eduardez/Oledukey/OLEDU_KiCad/OLEDUKEY/OLEDUKEY.csv

Reference | Value | Footprint | Datasheet | Part URL
U1 | STM32F072RBTx | Package_QFP:LQFP-64_10x10mm_P0.5mm | http://www.st.com/st-web-ui/static/active/en/resource/technical/document/datasheet/DM00090510.pdf | https://es.aliexpress.com/item/4001114352067.html
C1 | 100nF | Capacitor_SMD:C_0603_1608Metric_Pad1.08x0.95mm_HandSolder | https://datasheet.lcsc.com/lcsc/1809211526_FH-Guangdong-Fenghua-Advanced-Tech-0603F104M500NT_C42998.pdf | https://lcsc.com/product-detail/Multilayer-Ceramic-Capacitors-MLCC-SMD-SMT_FH-Guangdong-Fenghua-Advanced-Tech-0603F104M500NT_C42998.html
SW93 | Rotary_Encoder_Switch | Rotary_Encoder:RotaryEncoder_Alps_EC11E-Switch_Vertical_H20mm | https://www.farnell.com/datasheets/1837001.pdf | https://es.aliexpress.com/item/1744383771.html
C2 | 100nF | Capacitor_SMD:C_0603_1608Metric_Pad1.08x0.95mm_HandSolder | https://datasheet.lcsc.com/lcsc/1809211526_FH-Guangdong-Fenghua-Advanced-Tech-0603F104M500NT_C42998.pdf | https://lcsc.com/product-detail/Multilayer-Ceramic-Capacitors-MLCC-SMD-SMT_FH-Guangdong-Fenghua-Advanced-Tech-0603F104M500NT_C42998.html
SW92 | SW_Push | Button_Switch_SMD:SW_SPST_TL3342 | https://datasheet.lcsc.com/lcsc/2109061530_E-Switch-TL3342F160QG_C2886898.pdf | https://lcsc.com/product-detail/Tactile-Switches_E-Switch-TL3342F160QG_C2886898.html
R1 | 10k | Resistor_THT:R_Axial_DIN0204_L3.6mm_D1.6mm_P7.62mm_Horizontal | ~ | Home
C3 | 100nF | Capacitor_SMD:C_0603_1608Metric_Pad1.08x0.95mm_HandSolder | https://datasheet.lcsc.com/lcsc/1809211526_FH-Guangdong-Fenghua-Advanced-Tech-0603F104M500NT_C42998.pdf | https://lcsc.com/product-detail/Multilayer-Ceramic-Capacitors-MLCC-SMD-SMT_FH-Guangdong-Fenghua-Advanced-Tech-0603F104M500NT_C42998.html
SW91 | SW_Push | Button_Switch_SMD:SW_SPST_TL3342 | https://datasheet.lcsc.com/lcsc/2109061530_E-Switch-TL3342F160QG_C2886898.pdf | https://lcsc.com/product-detail/Tactile-Switches_E-Switch-TL3342F160QG_C2886898.html
R3 | 5.1k | Resistor_THT:R_Axial_DIN0204_L3.6mm_D1.6mm_P7.62mm_Horizontal | ~ | Home
R2 | 5.1k | Resistor_THT:R_Axial_DIN0204_L3.6mm_D1.6mm_P7.62mm_Horizontal | ~ | Home
J1 | USB_C_TYPE-C-31-M-12 | Connector_USB:USB_C_Receptacle_HRO_TYPE-C-31-M-12 | https://datasheet.lcsc.com/lcsc/2108131730_Korean-Hroparts-Elec-TYPE-C-31-M-12_C165948.pdf | https://lcsc.com/product-detail/USB-Connectors_Korean-Hroparts-Elec-TYPE-C-31-M-12_C165948.html
U2 | 2.42OLED | oLED:DIYMORE.CC |  | https://es.aliexpress.com/item/33023119677.html
SW94 | Rotary_Encoder_Switch | Rotary_Encoder:RotaryEncoder_Alps_EC11E-Switch_Vertical_H20mm | https://www.farnell.com/datasheets/1837001.pdf | https://es.aliexpress.com/item/1744383771.html
U3 | AMS1117-3.3 | Package_TO_SOT_SMD:SOT-223-3_TabPin2 | http://www.advanced-monolithic.com/pdf/ds1117.pdf | https://lcsc.com/product-detail/Linear-Voltage-Regulators-LDO_PUOLOP-AMS1117-3-3_C351784.html
C4 | 10uF | Capacitor_SMD:C_0603_1608Metric_Pad1.08x0.95mm_HandSolder | https://datasheet.lcsc.com/lcsc/1811021421_Samsung-Electro-Mechanics-CL10A106MP8NNNC_C85713.pdf | https://lcsc.com/product-detail/Multilayer-Ceramic-Capacitors-MLCC-SMD-SMT_Samsung-Electro-Mechanics-CL10A106MP8NNNC_C85713.html
C5 | 100nF | Capacitor_SMD:C_0603_1608Metric_Pad1.08x0.95mm_HandSolder | https://datasheet.lcsc.com/lcsc/1809211526_FH-Guangdong-Fenghua-Advanced-Tech-0603F104M500NT_C42998.pdf | https://lcsc.com/product-detail/Multilayer-Ceramic-Capacitors-MLCC-SMD-SMT_FH-Guangdong-Fenghua-Advanced-Tech-0603F104M500NT_C42998.html
C6 | 100nF | Capacitor_SMD:C_0603_1608Metric_Pad1.08x0.95mm_HandSolder | https://datasheet.lcsc.com/lcsc/1809211526_FH-Guangdong-Fenghua-Advanced-Tech-0603F104M500NT_C42998.pdf | https://lcsc.com/product-detail/Multilayer-Ceramic-Capacitors-MLCC-SMD-SMT_FH-Guangdong-Fenghua-Advanced-Tech-0603F104M500NT_C42998.html
C7 | 10uF | Capacitor_SMD:C_0603_1608Metric_Pad1.08x0.95mm_HandSolder | https://datasheet.lcsc.com/lcsc/1811021421_Samsung-Electro-Mechanics-CL10A106MP8NNNC_C85713.pdf | https://lcsc.com/product-detail/Multilayer-Ceramic-Capacitors-MLCC-SMD-SMT_Samsung-Electro-Mechanics-CL10A106MP8NNNC_C85713.html
RV1 | R_POT | Potentiometer_THT:Potentiometer_Bourns_PTA6043_Single_Slide | https://www.mouser.es/datasheet/2/54/pta-778345.pdf | https://es.aliexpress.com/item/32785393756.html
D311 | SK6812MINI | LED_SDM_MOD:SK6812-MINI-E | https://cdn-shop.adafruit.com/product-files/2686/SK6812MINI_REV.01-1-2.pdf | https://es.aliexpress.com/item/32782295214.html
D310 | SK6812MINI | LED_SDM_MOD:SK6812-MINI-E | https://cdn-shop.adafruit.com/product-files/2686/SK6812MINI_REV.01-1-2.pdf | https://es.aliexpress.com/item/32782295214.html
D309 | SK6812MINI | LED_SDM_MOD:SK6812-MINI-E | https://cdn-shop.adafruit.com/product-files/2686/SK6812MINI_REV.01-1-2.pdf | https://es.aliexpress.com/item/32782295214.html
D312 | SK6812MINI | LED_SDM_MOD:SK6812-MINI-E | https://cdn-shop.adafruit.com/product-files/2686/SK6812MINI_REV.01-1-2.pdf | https://es.aliexpress.com/item/32782295214.html
D316 | SK6812MINI | LED_SDM_MOD:SK6812-MINI-E | https://cdn-shop.adafruit.com/product-files/2686/SK6812MINI_REV.01-1-2.pdf | https://es.aliexpress.com/item/32782295214.html
D314 | SK6812MINI | LED_SDM_MOD:SK6812-MINI-E | https://cdn-shop.adafruit.com/product-files/2686/SK6812MINI_REV.01-1-2.pdf | https://es.aliexpress.com/item/32782295214.html
D315 | SK6812MINI | LED_SDM_MOD:SK6812-MINI-E | https://cdn-shop.adafruit.com/product-files/2686/SK6812MINI_REV.01-1-2.pdf | https://es.aliexpress.com/item/32782295214.html
D313 | SK6812MINI | LED_SDM_MOD:SK6812-MINI-E | https://cdn-shop.adafruit.com/product-files/2686/SK6812MINI_REV.01-1-2.pdf | https://es.aliexpress.com/item/32782295214.html
D319 | SK6812MINI | LED_SDM_MOD:SK6812-MINI-E | https://cdn-shop.adafruit.com/product-files/2686/SK6812MINI_REV.01-1-2.pdf | https://es.aliexpress.com/item/32782295214.html
D318 | SK6812MINI | LED_SDM_MOD:SK6812-MINI-E | https://cdn-shop.adafruit.com/product-files/2686/SK6812MINI_REV.01-1-2.pdf | https://es.aliexpress.com/item/32782295214.html
D317 | SK6812MINI | LED_SDM_MOD:SK6812-MINI-E | https://cdn-shop.adafruit.com/product-files/2686/SK6812MINI_REV.01-1-2.pdf | https://es.aliexpress.com/item/32782295214.html
D320 | SK6812MINI | LED_SDM_MOD:SK6812-MINI-E | https://cdn-shop.adafruit.com/product-files/2686/SK6812MINI_REV.01-1-2.pdf | https://es.aliexpress.com/item/32782295214.html
D324 | SK6812MINI | LED_SDM_MOD:SK6812-MINI-E | https://cdn-shop.adafruit.com/product-files/2686/SK6812MINI_REV.01-1-2.pdf | https://es.aliexpress.com/item/32782295214.html
D321 | SK6812MINI | LED_SDM_MOD:SK6812-MINI-E | https://cdn-shop.adafruit.com/product-files/2686/SK6812MINI_REV.01-1-2.pdf | https://es.aliexpress.com/item/32782295214.html
D322 | SK6812MINI | LED_SDM_MOD:SK6812-MINI-E | https://cdn-shop.adafruit.com/product-files/2686/SK6812MINI_REV.01-1-2.pdf | https://es.aliexpress.com/item/32782295214.html
D323 | SK6812MINI | LED_SDM_MOD:SK6812-MINI-E | https://cdn-shop.adafruit.com/product-files/2686/SK6812MINI_REV.01-1-2.pdf | https://es.aliexpress.com/item/32782295214.html
D327 | SK6812MINI | LED_SDM_MOD:SK6812-MINI-E | https://cdn-shop.adafruit.com/product-files/2686/SK6812MINI_REV.01-1-2.pdf | https://es.aliexpress.com/item/32782295214.html
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
D303 | SK6812MINI | LED_SDM_MOD:SK6812-MINI-E | https://cdn-shop.adafruit.com/product-files/2686/SK6812MINI_REV.01-1-2.pdf | https://es.aliexpress.com/item/32782295214.html
U301 | 74LVC1G125 | Package_TO_SOT_SMD:SOT-23-5 | https://datasheet.lcsc.com/lcsc/1809200051_Texas-Instruments-SN74LVC1G125DBVR_C23654.pdf | https://lcsc.com/product-detail/Buffers-Drivers_Texas-Instruments-SN74LVC1G125DBVR_C23654.html
C301 | 100nF | Capacitor_SMD:C_0603_1608Metric_Pad1.08x0.95mm_HandSolder | https://datasheet.lcsc.com/lcsc/1809211526_FH-Guangdong-Fenghua-Advanced-Tech-0603F104M500NT_C42998.pdf | https://lcsc.com/product-detail/Multilayer-Ceramic-Capacitors-MLCC-SMD-SMT_FH-Guangdong-Fenghua-Advanced-Tech-0603F104M500NT_C42998.html
C304 | 100nF | Capacitor_SMD:C_0603_1608Metric_Pad1.08x0.95mm_HandSolder | https://datasheet.lcsc.com/lcsc/1809211526_FH-Guangdong-Fenghua-Advanced-Tech-0603F104M500NT_C42998.pdf | https://lcsc.com/product-detail/Multilayer-Ceramic-Capacitors-MLCC-SMD-SMT_FH-Guangdong-Fenghua-Advanced-Tech-0603F104M500NT_C42998.html
C303 | 100nF | Capacitor_SMD:C_0603_1608Metric_Pad1.08x0.95mm_HandSolder | https://datasheet.lcsc.com/lcsc/1809211526_FH-Guangdong-Fenghua-Advanced-Tech-0603F104M500NT_C42998.pdf | https://lcsc.com/product-detail/Multilayer-Ceramic-Capacitors-MLCC-SMD-SMT_FH-Guangdong-Fenghua-Advanced-Tech-0603F104M500NT_C42998.html
C302 | 100nF | Capacitor_SMD:C_0603_1608Metric_Pad1.08x0.95mm_HandSolder | https://datasheet.lcsc.com/lcsc/1809211526_FH-Guangdong-Fenghua-Advanced-Tech-0603F104M500NT_C42998.pdf | https://lcsc.com/product-detail/Multilayer-Ceramic-Capacitors-MLCC-SMD-SMT_FH-Guangdong-Fenghua-Advanced-Tech-0603F104M500NT_C42998.html
C305 | 100nF | Capacitor_SMD:C_0603_1608Metric_Pad1.08x0.95mm_HandSolder | https://datasheet.lcsc.com/lcsc/1809211526_FH-Guangdong-Fenghua-Advanced-Tech-0603F104M500NT_C42998.pdf | https://lcsc.com/product-detail/Multilayer-Ceramic-Capacitors-MLCC-SMD-SMT_FH-Guangdong-Fenghua-Advanced-Tech-0603F104M500NT_C42998.html
C306 | 100nF | Capacitor_SMD:C_0603_1608Metric_Pad1.08x0.95mm_HandSolder | https://datasheet.lcsc.com/lcsc/1809211526_FH-Guangdong-Fenghua-Advanced-Tech-0603F104M500NT_C42998.pdf | https://lcsc.com/product-detail/Multilayer-Ceramic-Capacitors-MLCC-SMD-SMT_FH-Guangdong-Fenghua-Advanced-Tech-0603F104M500NT_C42998.html
C307 | 100nF | Capacitor_SMD:C_0603_1608Metric_Pad1.08x0.95mm_HandSolder | https://datasheet.lcsc.com/lcsc/1809211526_FH-Guangdong-Fenghua-Advanced-Tech-0603F104M500NT_C42998.pdf | https://lcsc.com/product-detail/Multilayer-Ceramic-Capacitors-MLCC-SMD-SMT_FH-Guangdong-Fenghua-Advanced-Tech-0603F104M500NT_C42998.html
C308 | 100nF | Capacitor_SMD:C_0603_1608Metric_Pad1.08x0.95mm_HandSolder | https://datasheet.lcsc.com/lcsc/1809211526_FH-Guangdong-Fenghua-Advanced-Tech-0603F104M500NT_C42998.pdf | https://lcsc.com/product-detail/Multilayer-Ceramic-Capacitors-MLCC-SMD-SMT_FH-Guangdong-Fenghua-Advanced-Tech-0603F104M500NT_C42998.html
C309 | 100nF | Capacitor_SMD:C_0603_1608Metric_Pad1.08x0.95mm_HandSolder | https://datasheet.lcsc.com/lcsc/1809211526_FH-Guangdong-Fenghua-Advanced-Tech-0603F104M500NT_C42998.pdf | https://lcsc.com/product-detail/Multilayer-Ceramic-Capacitors-MLCC-SMD-SMT_FH-Guangdong-Fenghua-Advanced-Tech-0603F104M500NT_C42998.html
C312 | 100nF | Capacitor_SMD:C_0603_1608Metric_Pad1.08x0.95mm_HandSolder | https://datasheet.lcsc.com/lcsc/1809211526_FH-Guangdong-Fenghua-Advanced-Tech-0603F104M500NT_C42998.pdf | https://lcsc.com/product-detail/Multilayer-Ceramic-Capacitors-MLCC-SMD-SMT_FH-Guangdong-Fenghua-Advanced-Tech-0603F104M500NT_C42998.html
C311 | 100nF | Capacitor_SMD:C_0603_1608Metric_Pad1.08x0.95mm_HandSolder | https://datasheet.lcsc.com/lcsc/1809211526_FH-Guangdong-Fenghua-Advanced-Tech-0603F104M500NT_C42998.pdf | https://lcsc.com/product-detail/Multilayer-Ceramic-Capacitors-MLCC-SMD-SMT_FH-Guangdong-Fenghua-Advanced-Tech-0603F104M500NT_C42998.html
C310 | 100nF | Capacitor_SMD:C_0603_1608Metric_Pad1.08x0.95mm_HandSolder | https://datasheet.lcsc.com/lcsc/1809211526_FH-Guangdong-Fenghua-Advanced-Tech-0603F104M500NT_C42998.pdf | https://lcsc.com/product-detail/Multilayer-Ceramic-Capacitors-MLCC-SMD-SMT_FH-Guangdong-Fenghua-Advanced-Tech-0603F104M500NT_C42998.html
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
C359 | 100nF | Capacitor_SMD:C_0603_1608Metric_Pad1.08x0.95mm_HandSolder | https://datasheet.lcsc.com/lcsc/1809211526_FH-Guangdong-Fenghua-Advanced-Tech-0603F104M500NT_C42998.pdf | https://lcsc.com/product-detail/Multilayer-Ceramic-Capacitors-MLCC-SMD-SMT_FH-Guangdong-Fenghua-Advanced-Tech-0603F104M500NT_C42998.html
C358 | 100nF | Capacitor_SMD:C_0603_1608Metric_Pad1.08x0.95mm_HandSolder | https://datasheet.lcsc.com/lcsc/1809211526_FH-Guangdong-Fenghua-Advanced-Tech-0603F104M500NT_C42998.pdf | https://lcsc.com/product-detail/Multilayer-Ceramic-Capacitors-MLCC-SMD-SMT_FH-Guangdong-Fenghua-Advanced-Tech-0603F104M500NT_C42998.html
C329 | 100nF | Capacitor_SMD:C_0603_1608Metric_Pad1.08x0.95mm_HandSolder | https://datasheet.lcsc.com/lcsc/1809211526_FH-Guangdong-Fenghua-Advanced-Tech-0603F104M500NT_C42998.pdf | https://lcsc.com/product-detail/Multilayer-Ceramic-Capacitors-MLCC-SMD-SMT_FH-Guangdong-Fenghua-Advanced-Tech-0603F104M500NT_C42998.html
C332 | 100nF | Capacitor_SMD:C_0603_1608Metric_Pad1.08x0.95mm_HandSolder | https://datasheet.lcsc.com/lcsc/1809211526_FH-Guangdong-Fenghua-Advanced-Tech-0603F104M500NT_C42998.pdf | https://lcsc.com/product-detail/Multilayer-Ceramic-Capacitors-MLCC-SMD-SMT_FH-Guangdong-Fenghua-Advanced-Tech-0603F104M500NT_C42998.html
C331 | 100nF | Capacitor_SMD:C_0603_1608Metric_Pad1.08x0.95mm_HandSolder | https://datasheet.lcsc.com/lcsc/1809211526_FH-Guangdong-Fenghua-Advanced-Tech-0603F104M500NT_C42998.pdf | https://lcsc.com/product-detail/Multilayer-Ceramic-Capacitors-MLCC-SMD-SMT_FH-Guangdong-Fenghua-Advanced-Tech-0603F104M500NT_C42998.html
C330 | 100nF | Capacitor_SMD:C_0603_1608Metric_Pad1.08x0.95mm_HandSolder | https://datasheet.lcsc.com/lcsc/1809211526_FH-Guangdong-Fenghua-Advanced-Tech-0603F104M500NT_C42998.pdf | https://lcsc.com/product-detail/Multilayer-Ceramic-Capacitors-MLCC-SMD-SMT_FH-Guangdong-Fenghua-Advanced-Tech-0603F104M500NT_C42998.html
D363 | SK6812MINI | LED_SDM_MOD:SK6812-MINI-E | https://cdn-shop.adafruit.com/product-files/2686/SK6812MINI_REV.01-1-2.pdf | https://es.aliexpress.com/item/32782295214.html
D362 | SK6812MINI | LED_SDM_MOD:SK6812-MINI-E | https://cdn-shop.adafruit.com/product-files/2686/SK6812MINI_REV.01-1-2.pdf | https://es.aliexpress.com/item/32782295214.html
D361 | SK6812MINI | LED_SDM_MOD:SK6812-MINI-E | https://cdn-shop.adafruit.com/product-files/2686/SK6812MINI_REV.01-1-2.pdf | https://es.aliexpress.com/item/32782295214.html
D364 | SK6812MINI | LED_SDM_MOD:SK6812-MINI-E | https://cdn-shop.adafruit.com/product-files/2686/SK6812MINI_REV.01-1-2.pdf | https://es.aliexpress.com/item/32782295214.html
D368 | SK6812MINI | LED_SDM_MOD:SK6812-MINI-E | https://cdn-shop.adafruit.com/product-files/2686/SK6812MINI_REV.01-1-2.pdf | https://es.aliexpress.com/item/32782295214.html
D365 | SK6812MINI | LED_SDM_MOD:SK6812-MINI-E | https://cdn-shop.adafruit.com/product-files/2686/SK6812MINI_REV.01-1-2.pdf | https://es.aliexpress.com/item/32782295214.html
D366 | SK6812MINI | LED_SDM_MOD:SK6812-MINI-E | https://cdn-shop.adafruit.com/product-files/2686/SK6812MINI_REV.01-1-2.pdf | https://es.aliexpress.com/item/32782295214.html
D367 | SK6812MINI | LED_SDM_MOD:SK6812-MINI-E | https://cdn-shop.adafruit.com/product-files/2686/SK6812MINI_REV.01-1-2.pdf | https://es.aliexpress.com/item/32782295214.html
D371 | SK6812MINI | LED_SDM_MOD:SK6812-MINI-E | https://cdn-shop.adafruit.com/product-files/2686/SK6812MINI_REV.01-1-2.pdf | https://es.aliexpress.com/item/32782295214.html
D370 | SK6812MINI | LED_SDM_MOD:SK6812-MINI-E | https://cdn-shop.adafruit.com/product-files/2686/SK6812MINI_REV.01-1-2.pdf | https://es.aliexpress.com/item/32782295214.html
D369 | SK6812MINI | LED_SDM_MOD:SK6812-MINI-E | https://cdn-shop.adafruit.com/product-files/2686/SK6812MINI_REV.01-1-2.pdf | https://es.aliexpress.com/item/32782295214.html
D372 | SK6812MINI | LED_SDM_MOD:SK6812-MINI-E | https://cdn-shop.adafruit.com/product-files/2686/SK6812MINI_REV.01-1-2.pdf | https://es.aliexpress.com/item/32782295214.html
C361 | 100nF | Capacitor_SMD:C_0603_1608Metric_Pad1.08x0.95mm_HandSolder | https://datasheet.lcsc.com/lcsc/1809211526_FH-Guangdong-Fenghua-Advanced-Tech-0603F104M500NT_C42998.pdf | https://lcsc.com/product-detail/Multilayer-Ceramic-Capacitors-MLCC-SMD-SMT_FH-Guangdong-Fenghua-Advanced-Tech-0603F104M500NT_C42998.html
C364 | 100nF | Capacitor_SMD:C_0603_1608Metric_Pad1.08x0.95mm_HandSolder | https://datasheet.lcsc.com/lcsc/1809211526_FH-Guangdong-Fenghua-Advanced-Tech-0603F104M500NT_C42998.pdf | https://lcsc.com/product-detail/Multilayer-Ceramic-Capacitors-MLCC-SMD-SMT_FH-Guangdong-Fenghua-Advanced-Tech-0603F104M500NT_C42998.html
C363 | 100nF | Capacitor_SMD:C_0603_1608Metric_Pad1.08x0.95mm_HandSolder | https://datasheet.lcsc.com/lcsc/1809211526_FH-Guangdong-Fenghua-Advanced-Tech-0603F104M500NT_C42998.pdf | https://lcsc.com/product-detail/Multilayer-Ceramic-Capacitors-MLCC-SMD-SMT_FH-Guangdong-Fenghua-Advanced-Tech-0603F104M500NT_C42998.html
C362 | 100nF | Capacitor_SMD:C_0603_1608Metric_Pad1.08x0.95mm_HandSolder | https://datasheet.lcsc.com/lcsc/1809211526_FH-Guangdong-Fenghua-Advanced-Tech-0603F104M500NT_C42998.pdf | https://lcsc.com/product-detail/Multilayer-Ceramic-Capacitors-MLCC-SMD-SMT_FH-Guangdong-Fenghua-Advanced-Tech-0603F104M500NT_C42998.html
C365 | 100nF | Capacitor_SMD:C_0603_1608Metric_Pad1.08x0.95mm_HandSolder | https://datasheet.lcsc.com/lcsc/1809211526_FH-Guangdong-Fenghua-Advanced-Tech-0603F104M500NT_C42998.pdf | https://lcsc.com/product-detail/Multilayer-Ceramic-Capacitors-MLCC-SMD-SMT_FH-Guangdong-Fenghua-Advanced-Tech-0603F104M500NT_C42998.html
C368 | 100nF | Capacitor_SMD:C_0603_1608Metric_Pad1.08x0.95mm_HandSolder | https://datasheet.lcsc.com/lcsc/1809211526_FH-Guangdong-Fenghua-Advanced-Tech-0603F104M500NT_C42998.pdf | https://lcsc.com/product-detail/Multilayer-Ceramic-Capacitors-MLCC-SMD-SMT_FH-Guangdong-Fenghua-Advanced-Tech-0603F104M500NT_C42998.html
C367 | 100nF | Capacitor_SMD:C_0603_1608Metric_Pad1.08x0.95mm_HandSolder | https://datasheet.lcsc.com/lcsc/1809211526_FH-Guangdong-Fenghua-Advanced-Tech-0603F104M500NT_C42998.pdf | https://lcsc.com/product-detail/Multilayer-Ceramic-Capacitors-MLCC-SMD-SMT_FH-Guangdong-Fenghua-Advanced-Tech-0603F104M500NT_C42998.html
C366 | 100nF | Capacitor_SMD:C_0603_1608Metric_Pad1.08x0.95mm_HandSolder | https://datasheet.lcsc.com/lcsc/1809211526_FH-Guangdong-Fenghua-Advanced-Tech-0603F104M500NT_C42998.pdf | https://lcsc.com/product-detail/Multilayer-Ceramic-Capacitors-MLCC-SMD-SMT_FH-Guangdong-Fenghua-Advanced-Tech-0603F104M500NT_C42998.html
C369 | 100nF | Capacitor_SMD:C_0603_1608Metric_Pad1.08x0.95mm_HandSolder | https://datasheet.lcsc.com/lcsc/1809211526_FH-Guangdong-Fenghua-Advanced-Tech-0603F104M500NT_C42998.pdf | https://lcsc.com/product-detail/Multilayer-Ceramic-Capacitors-MLCC-SMD-SMT_FH-Guangdong-Fenghua-Advanced-Tech-0603F104M500NT_C42998.html
C371 | 100nF | Capacitor_SMD:C_0603_1608Metric_Pad1.08x0.95mm_HandSolder | https://datasheet.lcsc.com/lcsc/1809211526_FH-Guangdong-Fenghua-Advanced-Tech-0603F104M500NT_C42998.pdf | https://lcsc.com/product-detail/Multilayer-Ceramic-Capacitors-MLCC-SMD-SMT_FH-Guangdong-Fenghua-Advanced-Tech-0603F104M500NT_C42998.html
C370 | 100nF | Capacitor_SMD:C_0603_1608Metric_Pad1.08x0.95mm_HandSolder | https://datasheet.lcsc.com/lcsc/1809211526_FH-Guangdong-Fenghua-Advanced-Tech-0603F104M500NT_C42998.pdf | https://lcsc.com/product-detail/Multilayer-Ceramic-Capacitors-MLCC-SMD-SMT_FH-Guangdong-Fenghua-Advanced-Tech-0603F104M500NT_C42998.html
C360 | 100nF | Capacitor_SMD:C_0603_1608Metric_Pad1.08x0.95mm_HandSolder | https://datasheet.lcsc.com/lcsc/1809211526_FH-Guangdong-Fenghua-Advanced-Tech-0603F104M500NT_C42998.pdf | https://lcsc.com/product-detail/Multilayer-Ceramic-Capacitors-MLCC-SMD-SMT_FH-Guangdong-Fenghua-Advanced-Tech-0603F104M500NT_C42998.html
C372 | 100nF | Capacitor_SMD:C_0603_1608Metric_Pad1.08x0.95mm_HandSolder | https://datasheet.lcsc.com/lcsc/1809211526_FH-Guangdong-Fenghua-Advanced-Tech-0603F104M500NT_C42998.pdf | https://lcsc.com/product-detail/Multilayer-Ceramic-Capacitors-MLCC-SMD-SMT_FH-Guangdong-Fenghua-Advanced-Tech-0603F104M500NT_C42998.html
D711 | SK6812MINI | LED_SDM_MOD:LED_SK6812MINI_PLCC4_3.5x3.5mm_P1.75mm | https://cdn-shop.adafruit.com/product-files/2686/SK6812MINI_REV.01-1-2.pdf | https://es.aliexpress.com/item/32782295214.html
D710 | SK6812MINI | LED_SDM_MOD:LED_SK6812MINI_PLCC4_3.5x3.5mm_P1.75mm | https://cdn-shop.adafruit.com/product-files/2686/SK6812MINI_REV.01-1-2.pdf | https://es.aliexpress.com/item/32782295214.html
D709 | SK6812MINI | LED_SDM_MOD:LED_SK6812MINI_PLCC4_3.5x3.5mm_P1.75mm | https://cdn-shop.adafruit.com/product-files/2686/SK6812MINI_REV.01-1-2.pdf | https://es.aliexpress.com/item/32782295214.html
D712 | SK6812MINI | LED_SDM_MOD:LED_SK6812MINI_PLCC4_3.5x3.5mm_P1.75mm | https://cdn-shop.adafruit.com/product-files/2686/SK6812MINI_REV.01-1-2.pdf | https://es.aliexpress.com/item/32782295214.html
D707 | SK6812MINI | LED_SDM_MOD:LED_SK6812MINI_PLCC4_3.5x3.5mm_P1.75mm | https://cdn-shop.adafruit.com/product-files/2686/SK6812MINI_REV.01-1-2.pdf | https://es.aliexpress.com/item/32782295214.html
D706 | SK6812MINI | LED_SDM_MOD:LED_SK6812MINI_PLCC4_3.5x3.5mm_P1.75mm | https://cdn-shop.adafruit.com/product-files/2686/SK6812MINI_REV.01-1-2.pdf | https://es.aliexpress.com/item/32782295214.html
D705 | SK6812MINI | LED_SDM_MOD:LED_SK6812MINI_PLCC4_3.5x3.5mm_P1.75mm | https://cdn-shop.adafruit.com/product-files/2686/SK6812MINI_REV.01-1-2.pdf | https://es.aliexpress.com/item/32782295214.html
D708 | SK6812MINI | LED_SDM_MOD:LED_SK6812MINI_PLCC4_3.5x3.5mm_P1.75mm | https://cdn-shop.adafruit.com/product-files/2686/SK6812MINI_REV.01-1-2.pdf | https://es.aliexpress.com/item/32782295214.html
D704 | SK6812MINI | LED_SDM_MOD:LED_SK6812MINI_PLCC4_3.5x3.5mm_P1.75mm | https://cdn-shop.adafruit.com/product-files/2686/SK6812MINI_REV.01-1-2.pdf | https://es.aliexpress.com/item/32782295214.html
D701 | SK6812MINI | LED_SDM_MOD:LED_SK6812MINI_PLCC4_3.5x3.5mm_P1.75mm | https://cdn-shop.adafruit.com/product-files/2686/SK6812MINI_REV.01-1-2.pdf | https://es.aliexpress.com/item/32782295214.html
D702 | SK6812MINI | LED_SDM_MOD:LED_SK6812MINI_PLCC4_3.5x3.5mm_P1.75mm | https://cdn-shop.adafruit.com/product-files/2686/SK6812MINI_REV.01-1-2.pdf | https://es.aliexpress.com/item/32782295214.html
D703 | SK6812MINI | LED_SDM_MOD:LED_SK6812MINI_PLCC4_3.5x3.5mm_P1.75mm | https://cdn-shop.adafruit.com/product-files/2686/SK6812MINI_REV.01-1-2.pdf | https://es.aliexpress.com/item/32782295214.html
D718 | SK6812MINI | LED_SDM_MOD:LED_SK6812MINI_PLCC4_3.5x3.5mm_P1.75mm | https://cdn-shop.adafruit.com/product-files/2686/SK6812MINI_REV.01-1-2.pdf | https://es.aliexpress.com/item/32782295214.html
D717 | SK6812MINI | LED_SDM_MOD:LED_SK6812MINI_PLCC4_3.5x3.5mm_P1.75mm | https://cdn-shop.adafruit.com/product-files/2686/SK6812MINI_REV.01-1-2.pdf | https://es.aliexpress.com/item/32782295214.html
D715 | SK6812MINI | LED_SDM_MOD:LED_SK6812MINI_PLCC4_3.5x3.5mm_P1.75mm | https://cdn-shop.adafruit.com/product-files/2686/SK6812MINI_REV.01-1-2.pdf | https://es.aliexpress.com/item/32782295214.html
D714 | SK6812MINI | LED_SDM_MOD:LED_SK6812MINI_PLCC4_3.5x3.5mm_P1.75mm | https://cdn-shop.adafruit.com/product-files/2686/SK6812MINI_REV.01-1-2.pdf | https://es.aliexpress.com/item/32782295214.html
D713 | SK6812MINI | LED_SDM_MOD:LED_SK6812MINI_PLCC4_3.5x3.5mm_P1.75mm | https://cdn-shop.adafruit.com/product-files/2686/SK6812MINI_REV.01-1-2.pdf | https://es.aliexpress.com/item/32782295214.html
D716 | SK6812MINI | LED_SDM_MOD:LED_SK6812MINI_PLCC4_3.5x3.5mm_P1.75mm | https://cdn-shop.adafruit.com/product-files/2686/SK6812MINI_REV.01-1-2.pdf | https://es.aliexpress.com/item/32782295214.html
J701 | Conn_01x03 | Connector_PinHeader_2.54mm:PinHeader_1x03_P2.54mm_Vertical | ~ | Home
U701 | 74LVC1G125 | Package_TO_SOT_SMD:SOT-23-5 | https://datasheet.lcsc.com/lcsc/1809200051_Texas-Instruments-SN74LVC1G125DBVR_C23654.pdf | https://lcsc.com/product-detail/Buffers-Drivers_Texas-Instruments-SN74LVC1G125DBVR_C23654.html
C701 | 100nF | Capacitor_SMD:C_0603_1608Metric_Pad1.08x0.95mm_HandSolder | https://datasheet.lcsc.com/lcsc/1809211526_FH-Guangdong-Fenghua-Advanced-Tech-0603F104M500NT_C42998.pdf | https://lcsc.com/product-detail/Multilayer-Ceramic-Capacitors-MLCC-SMD-SMT_FH-Guangdong-Fenghua-Advanced-Tech-0603F104M500NT_C42998.html
C704 | 100nF | Capacitor_SMD:C_0603_1608Metric_Pad1.08x0.95mm_HandSolder | https://datasheet.lcsc.com/lcsc/1809211526_FH-Guangdong-Fenghua-Advanced-Tech-0603F104M500NT_C42998.pdf | https://lcsc.com/product-detail/Multilayer-Ceramic-Capacitors-MLCC-SMD-SMT_FH-Guangdong-Fenghua-Advanced-Tech-0603F104M500NT_C42998.html
C703 | 100nF | Capacitor_SMD:C_0603_1608Metric_Pad1.08x0.95mm_HandSolder | https://datasheet.lcsc.com/lcsc/1809211526_FH-Guangdong-Fenghua-Advanced-Tech-0603F104M500NT_C42998.pdf | https://lcsc.com/product-detail/Multilayer-Ceramic-Capacitors-MLCC-SMD-SMT_FH-Guangdong-Fenghua-Advanced-Tech-0603F104M500NT_C42998.html
C702 | 100nF | Capacitor_SMD:C_0603_1608Metric_Pad1.08x0.95mm_HandSolder | https://datasheet.lcsc.com/lcsc/1809211526_FH-Guangdong-Fenghua-Advanced-Tech-0603F104M500NT_C42998.pdf | https://lcsc.com/product-detail/Multilayer-Ceramic-Capacitors-MLCC-SMD-SMT_FH-Guangdong-Fenghua-Advanced-Tech-0603F104M500NT_C42998.html
C705 | 100nF | Capacitor_SMD:C_0603_1608Metric_Pad1.08x0.95mm_HandSolder | https://datasheet.lcsc.com/lcsc/1809211526_FH-Guangdong-Fenghua-Advanced-Tech-0603F104M500NT_C42998.pdf | https://lcsc.com/product-detail/Multilayer-Ceramic-Capacitors-MLCC-SMD-SMT_FH-Guangdong-Fenghua-Advanced-Tech-0603F104M500NT_C42998.html
C708 | 100nF | Capacitor_SMD:C_0603_1608Metric_Pad1.08x0.95mm_HandSolder | https://datasheet.lcsc.com/lcsc/1809211526_FH-Guangdong-Fenghua-Advanced-Tech-0603F104M500NT_C42998.pdf | https://lcsc.com/product-detail/Multilayer-Ceramic-Capacitors-MLCC-SMD-SMT_FH-Guangdong-Fenghua-Advanced-Tech-0603F104M500NT_C42998.html
C707 | 100nF | Capacitor_SMD:C_0603_1608Metric_Pad1.08x0.95mm_HandSolder | https://datasheet.lcsc.com/lcsc/1809211526_FH-Guangdong-Fenghua-Advanced-Tech-0603F104M500NT_C42998.pdf | https://lcsc.com/product-detail/Multilayer-Ceramic-Capacitors-MLCC-SMD-SMT_FH-Guangdong-Fenghua-Advanced-Tech-0603F104M500NT_C42998.html
C706 | 100nF | Capacitor_SMD:C_0603_1608Metric_Pad1.08x0.95mm_HandSolder | https://datasheet.lcsc.com/lcsc/1809211526_FH-Guangdong-Fenghua-Advanced-Tech-0603F104M500NT_C42998.pdf | https://lcsc.com/product-detail/Multilayer-Ceramic-Capacitors-MLCC-SMD-SMT_FH-Guangdong-Fenghua-Advanced-Tech-0603F104M500NT_C42998.html
C709 | 100nF | Capacitor_SMD:C_0603_1608Metric_Pad1.08x0.95mm_HandSolder | https://datasheet.lcsc.com/lcsc/1809211526_FH-Guangdong-Fenghua-Advanced-Tech-0603F104M500NT_C42998.pdf | https://lcsc.com/product-detail/Multilayer-Ceramic-Capacitors-MLCC-SMD-SMT_FH-Guangdong-Fenghua-Advanced-Tech-0603F104M500NT_C42998.html
C712 | 100nF | Capacitor_SMD:C_0603_1608Metric_Pad1.08x0.95mm_HandSolder | https://datasheet.lcsc.com/lcsc/1809211526_FH-Guangdong-Fenghua-Advanced-Tech-0603F104M500NT_C42998.pdf | https://lcsc.com/product-detail/Multilayer-Ceramic-Capacitors-MLCC-SMD-SMT_FH-Guangdong-Fenghua-Advanced-Tech-0603F104M500NT_C42998.html
C711 | 100nF | Capacitor_SMD:C_0603_1608Metric_Pad1.08x0.95mm_HandSolder | https://datasheet.lcsc.com/lcsc/1809211526_FH-Guangdong-Fenghua-Advanced-Tech-0603F104M500NT_C42998.pdf | https://lcsc.com/product-detail/Multilayer-Ceramic-Capacitors-MLCC-SMD-SMT_FH-Guangdong-Fenghua-Advanced-Tech-0603F104M500NT_C42998.html
C710 | 100nF | Capacitor_SMD:C_0603_1608Metric_Pad1.08x0.95mm_HandSolder | https://datasheet.lcsc.com/lcsc/1809211526_FH-Guangdong-Fenghua-Advanced-Tech-0603F104M500NT_C42998.pdf | https://lcsc.com/product-detail/Multilayer-Ceramic-Capacitors-MLCC-SMD-SMT_FH-Guangdong-Fenghua-Advanced-Tech-0603F104M500NT_C42998.html
C713 | 100nF | Capacitor_SMD:C_0603_1608Metric_Pad1.08x0.95mm_HandSolder | https://datasheet.lcsc.com/lcsc/1809211526_FH-Guangdong-Fenghua-Advanced-Tech-0603F104M500NT_C42998.pdf | https://lcsc.com/product-detail/Multilayer-Ceramic-Capacitors-MLCC-SMD-SMT_FH-Guangdong-Fenghua-Advanced-Tech-0603F104M500NT_C42998.html
C716 | 100nF | Capacitor_SMD:C_0603_1608Metric_Pad1.08x0.95mm_HandSolder | https://datasheet.lcsc.com/lcsc/1809211526_FH-Guangdong-Fenghua-Advanced-Tech-0603F104M500NT_C42998.pdf | https://lcsc.com/product-detail/Multilayer-Ceramic-Capacitors-MLCC-SMD-SMT_FH-Guangdong-Fenghua-Advanced-Tech-0603F104M500NT_C42998.html
C715 | 100nF | Capacitor_SMD:C_0603_1608Metric_Pad1.08x0.95mm_HandSolder | https://datasheet.lcsc.com/lcsc/1809211526_FH-Guangdong-Fenghua-Advanced-Tech-0603F104M500NT_C42998.pdf | https://lcsc.com/product-detail/Multilayer-Ceramic-Capacitors-MLCC-SMD-SMT_FH-Guangdong-Fenghua-Advanced-Tech-0603F104M500NT_C42998.html
C714 | 100nF | Capacitor_SMD:C_0603_1608Metric_Pad1.08x0.95mm_HandSolder | https://datasheet.lcsc.com/lcsc/1809211526_FH-Guangdong-Fenghua-Advanced-Tech-0603F104M500NT_C42998.pdf | https://lcsc.com/product-detail/Multilayer-Ceramic-Capacitors-MLCC-SMD-SMT_FH-Guangdong-Fenghua-Advanced-Tech-0603F104M500NT_C42998.html
C717 | 100nF | Capacitor_SMD:C_0603_1608Metric_Pad1.08x0.95mm_HandSolder | https://datasheet.lcsc.com/lcsc/1809211526_FH-Guangdong-Fenghua-Advanced-Tech-0603F104M500NT_C42998.pdf | https://lcsc.com/product-detail/Multilayer-Ceramic-Capacitors-MLCC-SMD-SMT_FH-Guangdong-Fenghua-Advanced-Tech-0603F104M500NT_C42998.html
C718 | 100nF | Capacitor_SMD:C_0603_1608Metric_Pad1.08x0.95mm_HandSolder | https://datasheet.lcsc.com/lcsc/1809211526_FH-Guangdong-Fenghua-Advanced-Tech-0603F104M500NT_C42998.pdf | https://lcsc.com/product-detail/Multilayer-Ceramic-Capacitors-MLCC-SMD-SMT_FH-Guangdong-Fenghua-Advanced-Tech-0603F104M500NT_C42998.html
D375 | SK6812MINI | LED_SDM_MOD:SK6812-MINI-E | https://cdn-shop.adafruit.com/product-files/2686/SK6812MINI_REV.01-1-2.pdf | https://es.aliexpress.com/item/32782295214.html
D374 | SK6812MINI | LED_SDM_MOD:SK6812-MINI-E | https://cdn-shop.adafruit.com/product-files/2686/SK6812MINI_REV.01-1-2.pdf | https://es.aliexpress.com/item/32782295214.html
D373 | SK6812MINI | LED_SDM_MOD:SK6812-MINI-E | https://cdn-shop.adafruit.com/product-files/2686/SK6812MINI_REV.01-1-2.pdf | https://es.aliexpress.com/item/32782295214.html
D376 | SK6812MINI | LED_SDM_MOD:SK6812-MINI-E | https://cdn-shop.adafruit.com/product-files/2686/SK6812MINI_REV.01-1-2.pdf | https://es.aliexpress.com/item/32782295214.html
D380 | SK6812MINI | LED_SDM_MOD:SK6812-MINI-E | https://cdn-shop.adafruit.com/product-files/2686/SK6812MINI_REV.01-1-2.pdf | https://es.aliexpress.com/item/32782295214.html
D377 | SK6812MINI | LED_SDM_MOD:SK6812-MINI-E | https://cdn-shop.adafruit.com/product-files/2686/SK6812MINI_REV.01-1-2.pdf | https://es.aliexpress.com/item/32782295214.html
D378 | SK6812MINI | LED_SDM_MOD:SK6812-MINI-E | https://cdn-shop.adafruit.com/product-files/2686/SK6812MINI_REV.01-1-2.pdf | https://es.aliexpress.com/item/32782295214.html
D379 | SK6812MINI | LED_SDM_MOD:SK6812-MINI-E | https://cdn-shop.adafruit.com/product-files/2686/SK6812MINI_REV.01-1-2.pdf | https://es.aliexpress.com/item/32782295214.html
D383 | SK6812MINI | LED_SDM_MOD:SK6812-MINI-E | https://cdn-shop.adafruit.com/product-files/2686/SK6812MINI_REV.01-1-2.pdf | https://es.aliexpress.com/item/32782295214.html
D382 | SK6812MINI | LED_SDM_MOD:SK6812-MINI-E | https://cdn-shop.adafruit.com/product-files/2686/SK6812MINI_REV.01-1-2.pdf | https://es.aliexpress.com/item/32782295214.html
D381 | SK6812MINI | LED_SDM_MOD:SK6812-MINI-E | https://cdn-shop.adafruit.com/product-files/2686/SK6812MINI_REV.01-1-2.pdf | https://es.aliexpress.com/item/32782295214.html
D384 | SK6812MINI | LED_SDM_MOD:SK6812-MINI-E | https://cdn-shop.adafruit.com/product-files/2686/SK6812MINI_REV.01-1-2.pdf | https://es.aliexpress.com/item/32782295214.html
C373 | 100nF | Capacitor_SMD:C_0603_1608Metric_Pad1.08x0.95mm_HandSolder | https://datasheet.lcsc.com/lcsc/1809211526_FH-Guangdong-Fenghua-Advanced-Tech-0603F104M500NT_C42998.pdf | https://lcsc.com/product-detail/Multilayer-Ceramic-Capacitors-MLCC-SMD-SMT_FH-Guangdong-Fenghua-Advanced-Tech-0603F104M500NT_C42998.html
C376 | 100nF | Capacitor_SMD:C_0603_1608Metric_Pad1.08x0.95mm_HandSolder | https://datasheet.lcsc.com/lcsc/1809211526_FH-Guangdong-Fenghua-Advanced-Tech-0603F104M500NT_C42998.pdf | https://lcsc.com/product-detail/Multilayer-Ceramic-Capacitors-MLCC-SMD-SMT_FH-Guangdong-Fenghua-Advanced-Tech-0603F104M500NT_C42998.html
C375 | 100nF | Capacitor_SMD:C_0603_1608Metric_Pad1.08x0.95mm_HandSolder | https://datasheet.lcsc.com/lcsc/1809211526_FH-Guangdong-Fenghua-Advanced-Tech-0603F104M500NT_C42998.pdf | https://lcsc.com/product-detail/Multilayer-Ceramic-Capacitors-MLCC-SMD-SMT_FH-Guangdong-Fenghua-Advanced-Tech-0603F104M500NT_C42998.html
C374 | 100nF | Capacitor_SMD:C_0603_1608Metric_Pad1.08x0.95mm_HandSolder | https://datasheet.lcsc.com/lcsc/1809211526_FH-Guangdong-Fenghua-Advanced-Tech-0603F104M500NT_C42998.pdf | https://lcsc.com/product-detail/Multilayer-Ceramic-Capacitors-MLCC-SMD-SMT_FH-Guangdong-Fenghua-Advanced-Tech-0603F104M500NT_C42998.html
C377 | 100nF | Capacitor_SMD:C_0603_1608Metric_Pad1.08x0.95mm_HandSolder | https://datasheet.lcsc.com/lcsc/1809211526_FH-Guangdong-Fenghua-Advanced-Tech-0603F104M500NT_C42998.pdf | https://lcsc.com/product-detail/Multilayer-Ceramic-Capacitors-MLCC-SMD-SMT_FH-Guangdong-Fenghua-Advanced-Tech-0603F104M500NT_C42998.html
C380 | 100nF | Capacitor_SMD:C_0603_1608Metric_Pad1.08x0.95mm_HandSolder | https://datasheet.lcsc.com/lcsc/1809211526_FH-Guangdong-Fenghua-Advanced-Tech-0603F104M500NT_C42998.pdf | https://lcsc.com/product-detail/Multilayer-Ceramic-Capacitors-MLCC-SMD-SMT_FH-Guangdong-Fenghua-Advanced-Tech-0603F104M500NT_C42998.html
C379 | 100nF | Capacitor_SMD:C_0603_1608Metric_Pad1.08x0.95mm_HandSolder | https://datasheet.lcsc.com/lcsc/1809211526_FH-Guangdong-Fenghua-Advanced-Tech-0603F104M500NT_C42998.pdf | https://lcsc.com/product-detail/Multilayer-Ceramic-Capacitors-MLCC-SMD-SMT_FH-Guangdong-Fenghua-Advanced-Tech-0603F104M500NT_C42998.html
C378 | 100nF | Capacitor_SMD:C_0603_1608Metric_Pad1.08x0.95mm_HandSolder | https://datasheet.lcsc.com/lcsc/1809211526_FH-Guangdong-Fenghua-Advanced-Tech-0603F104M500NT_C42998.pdf | https://lcsc.com/product-detail/Multilayer-Ceramic-Capacitors-MLCC-SMD-SMT_FH-Guangdong-Fenghua-Advanced-Tech-0603F104M500NT_C42998.html
C381 | 100nF | Capacitor_SMD:C_0603_1608Metric_Pad1.08x0.95mm_HandSolder | https://datasheet.lcsc.com/lcsc/1809211526_FH-Guangdong-Fenghua-Advanced-Tech-0603F104M500NT_C42998.pdf | https://lcsc.com/product-detail/Multilayer-Ceramic-Capacitors-MLCC-SMD-SMT_FH-Guangdong-Fenghua-Advanced-Tech-0603F104M500NT_C42998.html
C383 | 100nF | Capacitor_SMD:C_0603_1608Metric_Pad1.08x0.95mm_HandSolder | https://datasheet.lcsc.com/lcsc/1809211526_FH-Guangdong-Fenghua-Advanced-Tech-0603F104M500NT_C42998.pdf | https://lcsc.com/product-detail/Multilayer-Ceramic-Capacitors-MLCC-SMD-SMT_FH-Guangdong-Fenghua-Advanced-Tech-0603F104M500NT_C42998.html
C382 | 100nF | Capacitor_SMD:C_0603_1608Metric_Pad1.08x0.95mm_HandSolder | https://datasheet.lcsc.com/lcsc/1809211526_FH-Guangdong-Fenghua-Advanced-Tech-0603F104M500NT_C42998.pdf | https://lcsc.com/product-detail/Multilayer-Ceramic-Capacitors-MLCC-SMD-SMT_FH-Guangdong-Fenghua-Advanced-Tech-0603F104M500NT_C42998.html
C384 | 100nF | Capacitor_SMD:C_0603_1608Metric_Pad1.08x0.95mm_HandSolder | https://datasheet.lcsc.com/lcsc/1809211526_FH-Guangdong-Fenghua-Advanced-Tech-0603F104M500NT_C42998.pdf | https://lcsc.com/product-detail/Multilayer-Ceramic-Capacitors-MLCC-SMD-SMT_FH-Guangdong-Fenghua-Advanced-Tech-0603F104M500NT_C42998.html
J301 | Conn_01x03 | Connector_PinHeader_2.54mm:PinHeader_1x03_P2.54mm_Vertical | ~ | Home
D386 | SK6812MINI | LED_SDM_MOD:SK6812-MINI-E | https://cdn-shop.adafruit.com/product-files/2686/SK6812MINI_REV.01-1-2.pdf | https://es.aliexpress.com/item/32782295214.html
D385 | SK6812MINI | LED_SDM_MOD:SK6812-MINI-E | https://cdn-shop.adafruit.com/product-files/2686/SK6812MINI_REV.01-1-2.pdf | https://es.aliexpress.com/item/32782295214.html
C385 | 100nF | Capacitor_SMD:C_0603_1608Metric_Pad1.08x0.95mm_HandSolder | https://datasheet.lcsc.com/lcsc/1809211526_FH-Guangdong-Fenghua-Advanced-Tech-0603F104M500NT_C42998.pdf | https://lcsc.com/product-detail/Multilayer-Ceramic-Capacitors-MLCC-SMD-SMT_FH-Guangdong-Fenghua-Advanced-Tech-0603F104M500NT_C42998.html
C386 | 100nF | Capacitor_SMD:C_0603_1608Metric_Pad1.08x0.95mm_HandSolder | https://datasheet.lcsc.com/lcsc/1809211526_FH-Guangdong-Fenghua-Advanced-Tech-0603F104M500NT_C42998.pdf | https://lcsc.com/product-detail/Multilayer-Ceramic-Capacitors-MLCC-SMD-SMT_FH-Guangdong-Fenghua-Advanced-Tech-0603F104M500NT_C42998.html
SW85 | SW_Push | custom_keys:SW_Cherry_MX_1.00u_PCB | ~
SW90 | SW_Push | custom_keys:SW_Cherry_MX_1.00u_PCB | ~
SW89 | SW_Push | custom_keys:SW_Cherry_MX_1.00u_PCB | ~
SW88 | SW_Push | custom_keys:SW_Cherry_MX_1.00u_PCB | ~
SW87 | SW_Push | custom_keys:SW_Cherry_MX_1.00u_PCB | ~
SW86 | SW_Push | custom_keys:SW_Cherry_MX_1.00u_PCB | ~
SW79 | SW_Push | custom_keys:SW_Cherry_MX_1.00u_PCB | ~
SW84 | SW_Push | custom_keys:SW_Cherry_MX_1.00u_PCB | ~
SW83 | SW_Push | custom_keys:SW_Cherry_MX_1.00u_PCB | ~
SW82 | SW_Push | custom_keys:SW_Cherry_MX_2.25u_PCB | ~
SW81 | SW_Push | custom_keys:SW_Cherry_MX_1.50u_PCB | ~
SW80 | SW_Push | custom_keys:SW_Cherry_MX_2.00u_PCB | ~
SW73 | SW_Push | custom_keys:SW_Cherry_MX_1.00u_PCB | ~
SW76 | SW_Push | custom_keys:SW_Cherry_MX_1.00u_PCB | ~
SW75 | SW_Push | custom_keys:SW_Cherry_MX_1.00u_PCB | ~
SW74 | SW_Push | custom_keys:SW_Cherry_MX_1.00u_PCB | ~
SW67 | SW_Push | custom_keys:SW_Cherry_MX_1.00u_PCB | ~
SW72 | SW_Push | custom_keys:SW_Cherry_MX_1.00u_PCB | ~
SW71 | SW_Push | custom_keys:SW_Cherry_MX_1.75u_PCB | ~
SW70 | SW_Push | custom_keys:SW_Cherry_MX_1.00u_PCB | ~
SW69 | SW_Push | custom_keys:SW_Cherry_MX_1.00u_PCB | ~
SW68 | SW_Push | custom_keys:SW_Cherry_MX_1.00u_PCB | ~
SW61 | SW_Push | custom_keys:SW_Cherry_MX_1.00u_PCB | ~
SW66 | SW_Push | custom_keys:SW_Cherry_MX_1.00u_PCB | ~
SW65 | SW_Push | custom_keys:SW_Cherry_MX_1.00u_PCB | ~
SW64 | SW_Push | custom_keys:SW_Cherry_MX_1.00u_PCB | ~
SW63 | SW_Push | custom_keys:SW_Cherry_MX_1.00u_PCB | ~
SW62 | SW_Push | custom_keys:SW_Cherry_MX_1.00u_PCB | ~
SW55 | SW_Push | custom_keys:SW_Cherry_MX_1.00u_PCB | ~
SW60 | SW_Push | custom_keys:SW_Cherry_MX_1.00u_PCB | ~
SW59 | SW_Push | custom_keys:SW_Cherry_MX_1.00u_PCB | ~
SW58 | SW_Push | custom_keys:SW_Cherry_MX_1.00u_PCB | ~
SW57 | SW_Push | custom_keys:SW_Cherry_MX_1.00u_PCB | ~
SW56 | SW_Push | custom_keys:SW_Cherry_MX_1.00u_PCB | ~
SW49 | SW_Push | custom_keys:SW_Cherry_MX_1.00u_PCB | ~
SW54 | SW_Push | custom_keys:SW_Cherry_MX_1.00u_PCB | ~
SW53 | SW_Push | custom_keys:SW_Cherry_MX_1.00u_PCB | ~
SW52 | SW_Push | custom_keys:SW_Cherry_MX_1.00u_PCB | ~
SW51 | SW_Push | custom_keys:SW_Cherry_MX_1.00u_PCB | ~
SW50 | SW_Push | custom_keys:SW_Cherry_MX_1.00u_PCB | ~
SW43 | SW_Push | custom_keys:SW_Cherry_MX_1.00u_PCB | ~
SW47 | SW_Push | custom_keys:SW_Cherry_MX_1.00u_PCB | ~
SW46 | SW_Push | custom_keys:SW_Cherry_MX_1.00u_PCB | ~
SW45 | SW_Push | custom_keys:SW_Cherry_MX_1.00u_PCB | ~
SW44 | SW_Push | custom_keys:SW_Cherry_MX_1.00u_PCB | ~
SW37 | SW_Push | custom_keys:SW_Cherry_MX_1.00u_PCB | ~
SW41 | SW_Push | custom_keys:SW_Cherry_MX_1.00u_PCB | ~
SW40 | SW_Push | custom_keys:SW_Cherry_MX_1.00u_PCB | ~
SW39 | SW_Push | custom_keys:SW_Cherry_MX_1.00u_PCB | ~
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
D1 | 1N4148WS | Diode_SMD:D_0603_1608Metric | https://datasheet.lcsc.com/lcsc/1811131825_Shikues-1N4148WS_C110221.pdf | https://lcsc.com/product-detail/Switching-Diode_Shikues-1N4148WS_C110221.html
